ByTechLab/RF---Mostly-3D-Printed-Discone-Antenna/PROJECT_FILES/ECAD/15_DISCONE_V4/1_DISC_PCB_KICAD/_EXPORTED_RENDERS/DISC_PCB_TOP.png

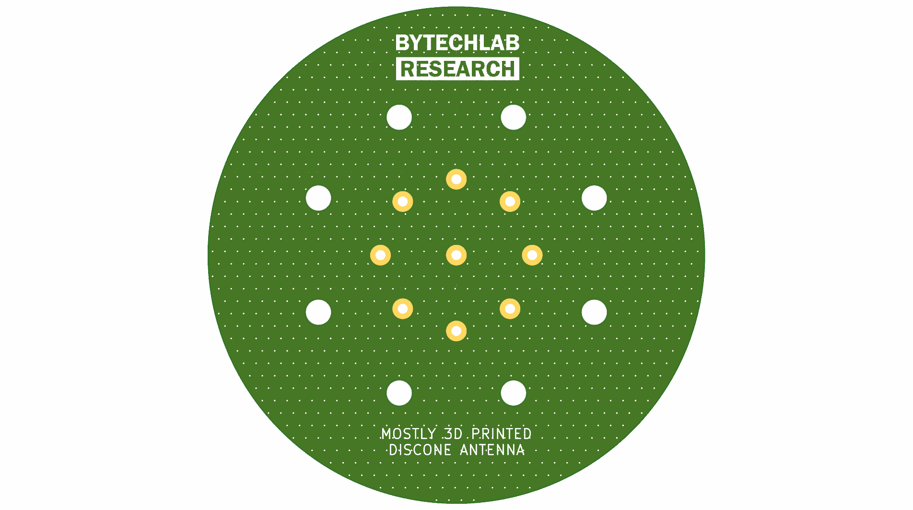
PROJECT_FILES/ECAD/15_DISCONE_V4/1_DISC_PCB_KICAD/_EXPORTED_RENDERS/DISC_PCB_TOP.png
