ByTechLab/RF---Mostly-3D-Printed-Discone-Antenna/PROJECT_FILES/ECAD/15_DISCONE_V4/2_CONE_PCB_KICAD/_EXPORTED_RENDERS/CONE_PCB_TOP.png

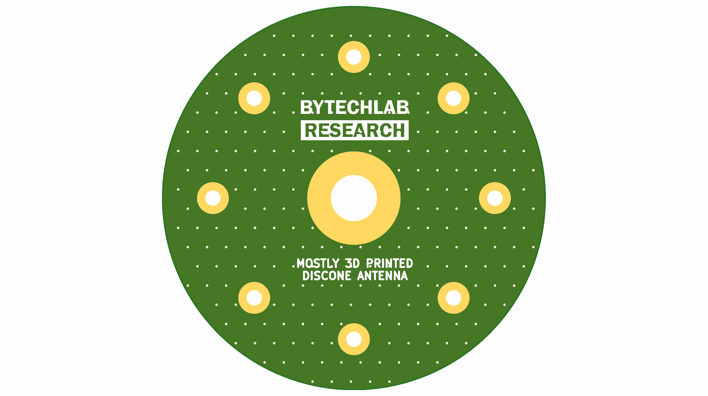
PROJECT_FILES/ECAD/15_DISCONE_V4/2_CONE_PCB_KICAD/_EXPORTED_RENDERS/CONE_PCB_TOP.png
