ByTechLab/RF---Mostly-3D-Printed-Discone-Antenna/PROJECT_FILES/ECAD/15_DISCONE_V4/3_PREAMP_PCB_KICAD/_EXPORTED_RENDERS/PREAMP_PCB_BOTTOM.png

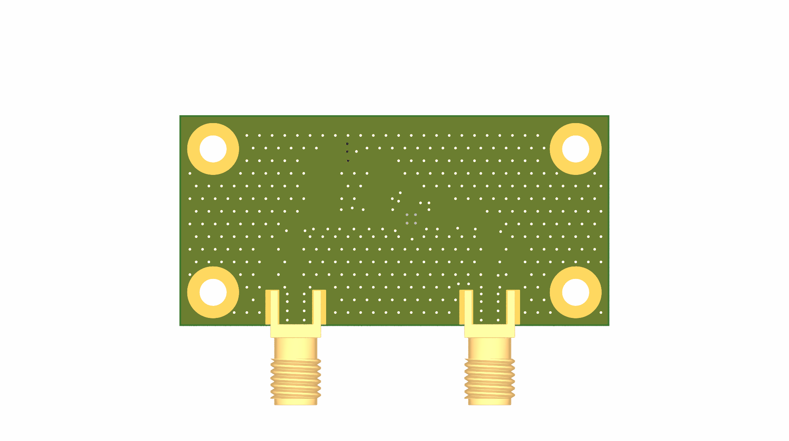
PROJECT_FILES/ECAD/15_DISCONE_V4/3_PREAMP_PCB_KICAD/_EXPORTED_RENDERS/PREAMP_PCB_BOTTOM.png
