ByTechLab/RF---Mostly-3D-Printed-Discone-Antenna/PROJECT_FILES/ECAD/15_DISCONE_V4/4_BIAS_TEE_PCB_KICAD/_EXPORTED_RENDERS/BIAS_TEE_PCB_BOTTOM.png

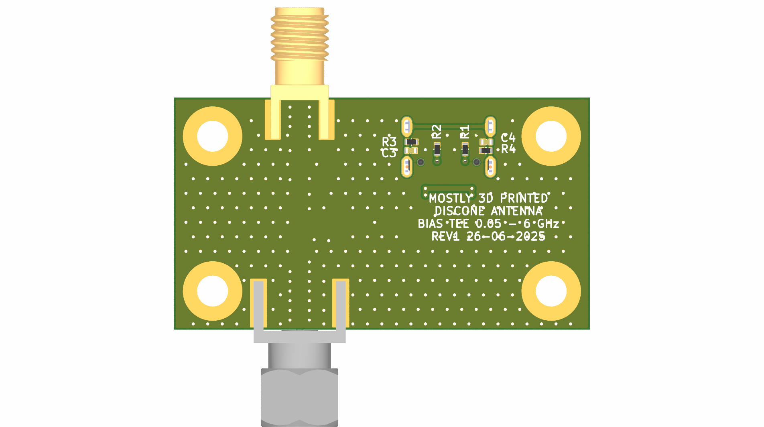
PROJECT_FILES/ECAD/15_DISCONE_V4/4_BIAS_TEE_PCB_KICAD/_EXPORTED_RENDERS/BIAS_TEE_PCB_BOTTOM.png
