ByTechLab/RF---Mostly-3D-Printed-Discone-Antenna/PROJECT_FILES/MCAD/15_DISCONE_V4_KICAD/_STL_EXPORTED/3DP_ASA_Mast_Mount.stl

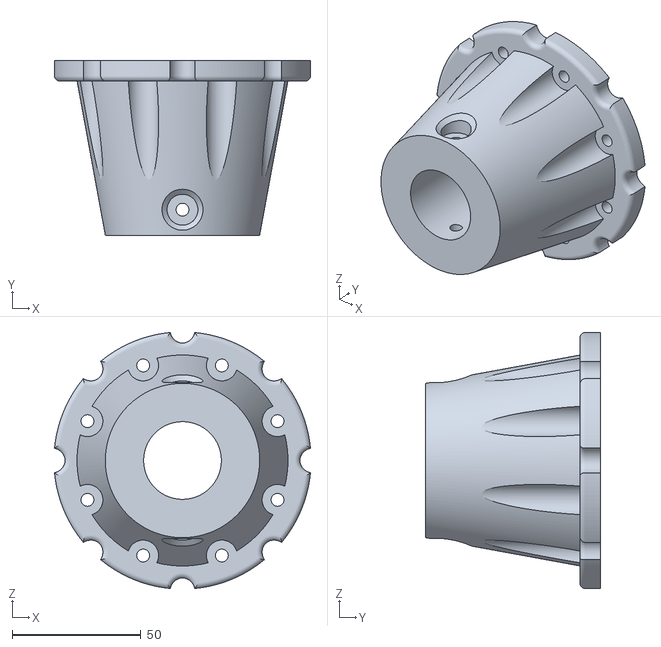
[picture p25: CAD file, 2025-08-10]
PROJECT_FILES/MCAD/15_DISCONE_V4_KICAD/_STL_EXPORTED/3DP_ASA_Mast_Mount.stl
99.5 x 68.0 x 99.5
