ByTechLab/RF---Mostly-3D-Printed-Discone-Antenna/PROJECT_FILES/MCAD/15_DISCONE_V4_KICAD/_STL_EXPORTED/3DP_ASA_Cone_and_Disc_Mount.stl

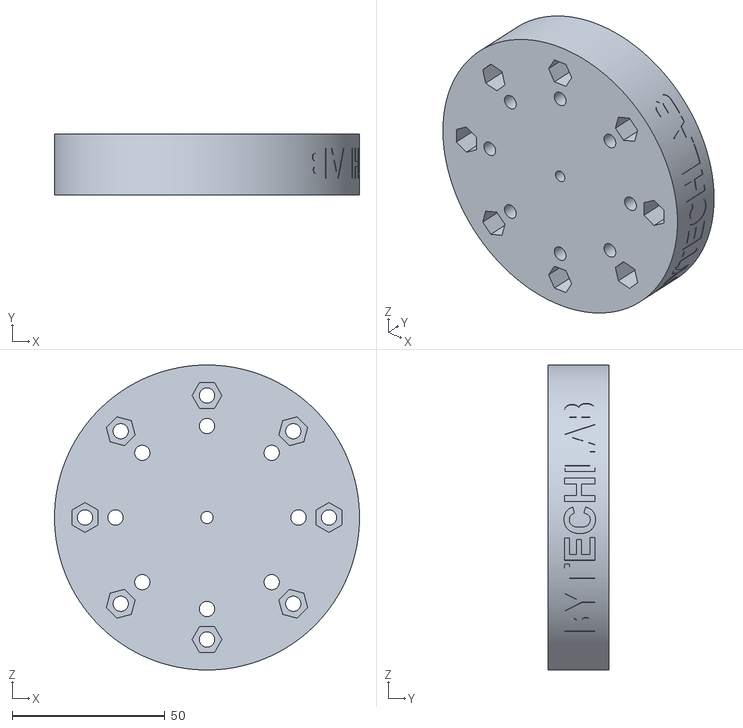
[picture p26: CAD file, 2025-08-10]
PROJECT_FILES/MCAD/15_DISCONE_V4_KICAD/_STL_EXPORTED/3DP_ASA_Cone_and_Disc_Mount.stl
100.0 x 20.0 x 100.0
