ByTechLab/RF---Mostly-3D-Printed-Discone-Antenna/PROJECT_FILES/MCAD/15_DISCONE_V4_KICAD/_STL_EXPORTED/3DP_ASA_Preamp_Case_Bottom.stl

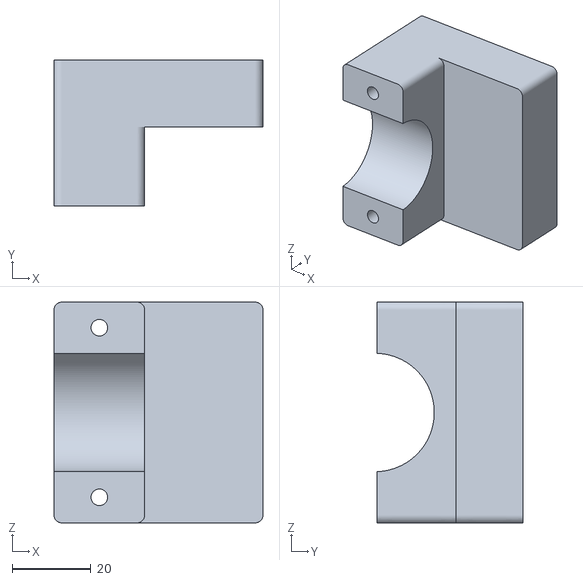
[picture p27: CAD file, 2025-08-10]
PROJECT_FILES/MCAD/15_DISCONE_V4_KICAD/_STL_EXPORTED/3DP_ASA_Preamp_Case_Bottom.stl
53.0 x 37.0 x 56.0
