ByTechLab/RF---Mostly-3D-Printed-Discone-Antenna/PROJECT_FILES/MCAD/15_DISCONE_V4_KICAD/_STL_EXPORTED/3DP_ASA_Preamp_Case_Top.stl

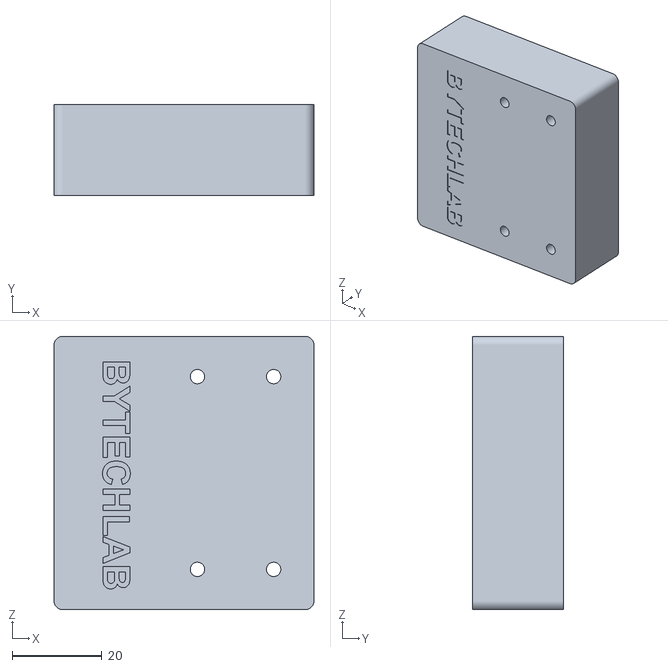
[picture p28: CAD file, 2025-08-10]
PROJECT_FILES/MCAD/15_DISCONE_V4_KICAD/_STL_EXPORTED/3DP_ASA_Preamp_Case_Top.stl
58.0 x 20.2 x 61.0
