ByTechLab/RF---Mostly-3D-Printed-Discone-Antenna/PROJECT_FILES/MCAD/15_DISCONE_V4_KICAD/_STL_EXPORTED/3DP_ASA_Balcony_Mounting_Clamp_Mid.stl

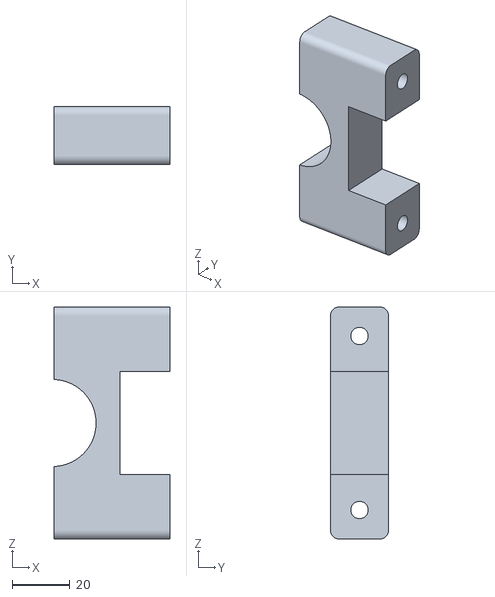
[picture p29: CAD file, 2025-08-10]
PROJECT_FILES/MCAD/15_DISCONE_V4_KICAD/_STL_EXPORTED/3DP_ASA_Balcony_Mounting_Clamp_Mid.stl
40.0 x 20.0 x 80.0
