ByTechLab/RF---Mostly-3D-Printed-Discone-Antenna/PROJECT_FILES/MEASUREMENTS/15_DISCONE_V4/ANT_CABLE_RG58_CU_S21.png

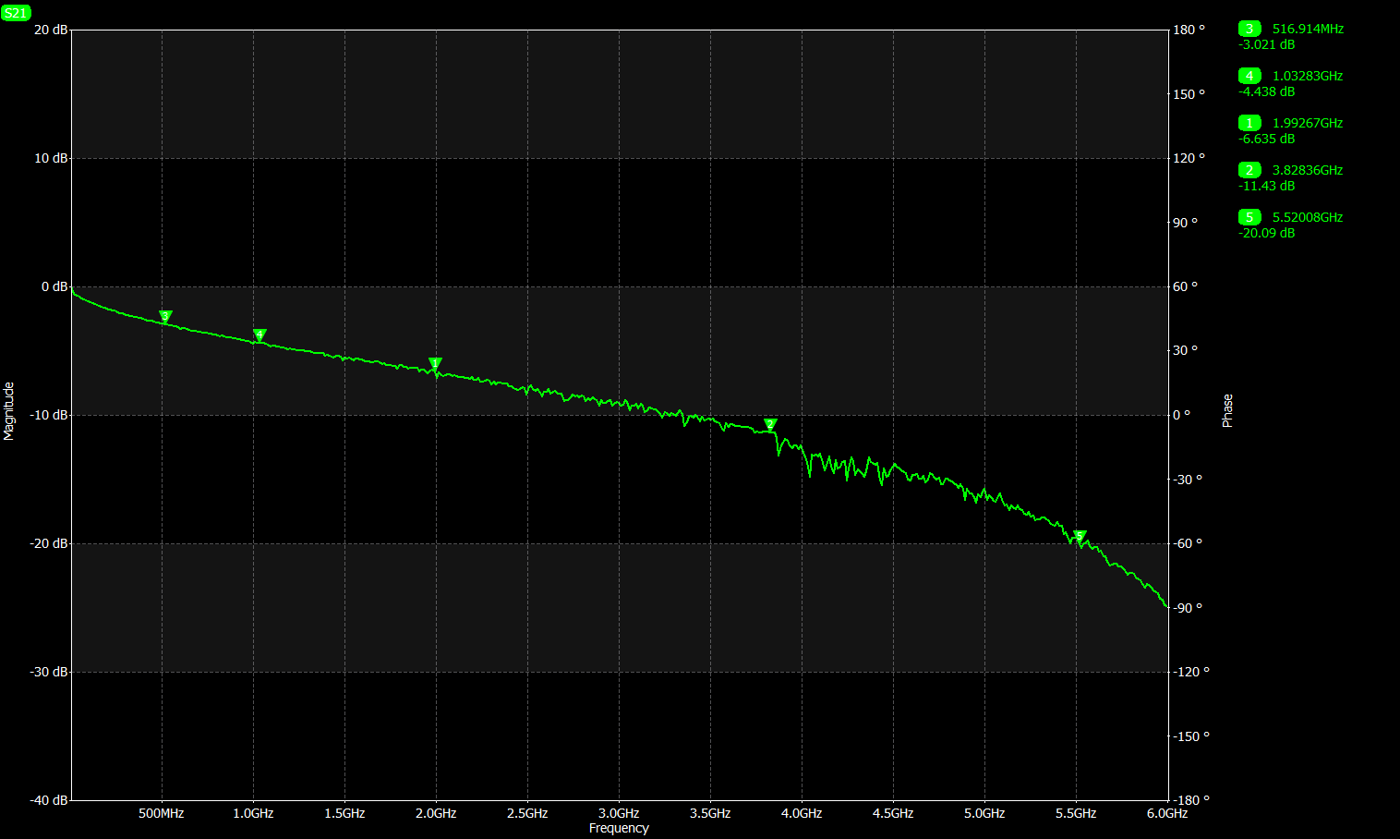
PROJECT_FILES/MEASUREMENTS/15_DISCONE_V4/ANT_CABLE_RG58_CU_S21.png
