ByTechLab/RF---Mostly-3D-Printed-Discone-Antenna/PROJECT_FILES/MEASUREMENTS/15_DISCONE_V4/PREAMP_PCB_MEAS_S11_S22_LOGMAG.png

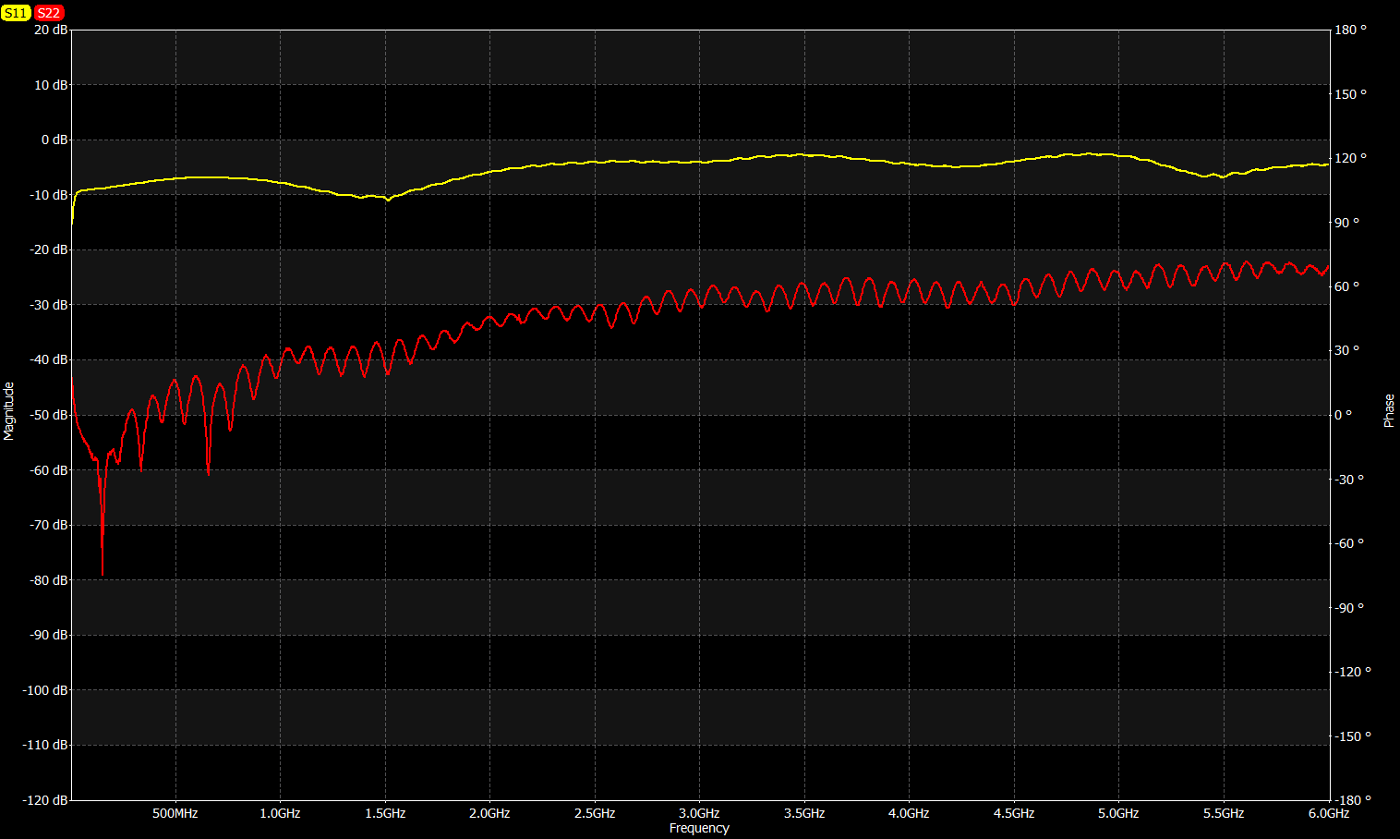
PROJECT_FILES/MEASUREMENTS/15_DISCONE_V4/PREAMP_PCB_MEAS_S11_S22_LOGMAG.png
