ByTechLab/RF---Mostly-3D-Printed-Discone-Antenna/PROJECT_FILES/MEASUREMENTS/15_DISCONE_V4/SDR_2400MHZ.png

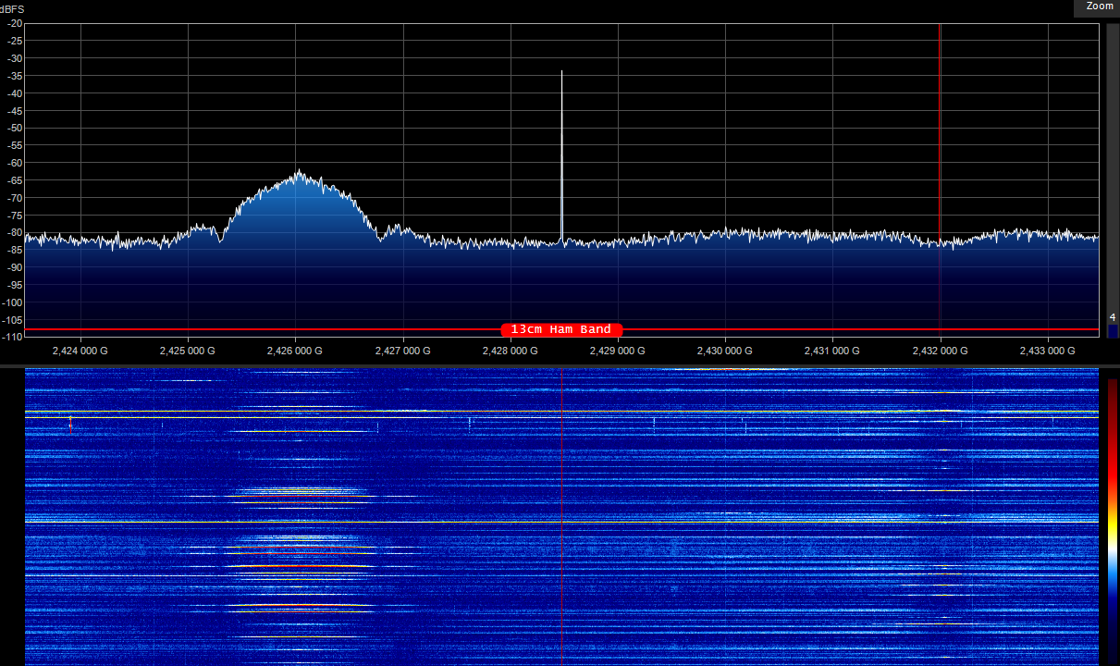
PROJECT_FILES/MEASUREMENTS/15_DISCONE_V4/SDR_2400MHZ.png
