ByTechLab/RF---Mostly-3D-Printed-Discone-Antenna/PROJECT_FILES/ECAD/15_DISCONE_V4/4_BIAS_TEE_PCB_KICAD/_EXPORTED_PDF/PCB/BIAS_TEE_PCB.pdf

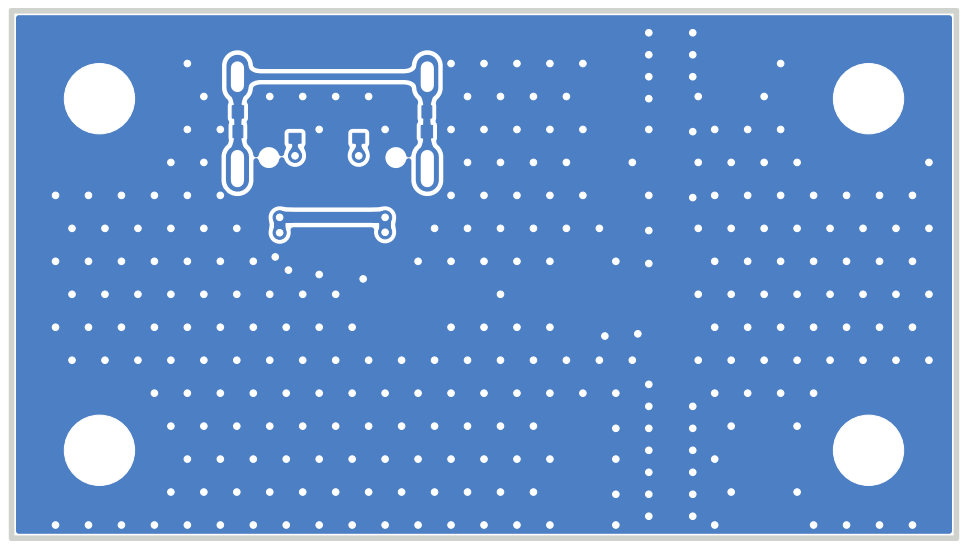
[picture p53: page 1]

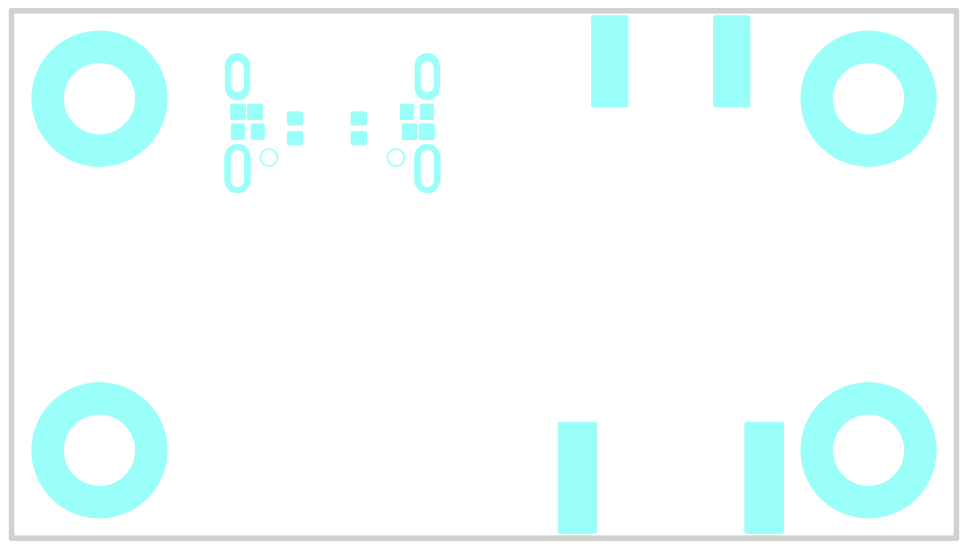
[picture p54: page 2]

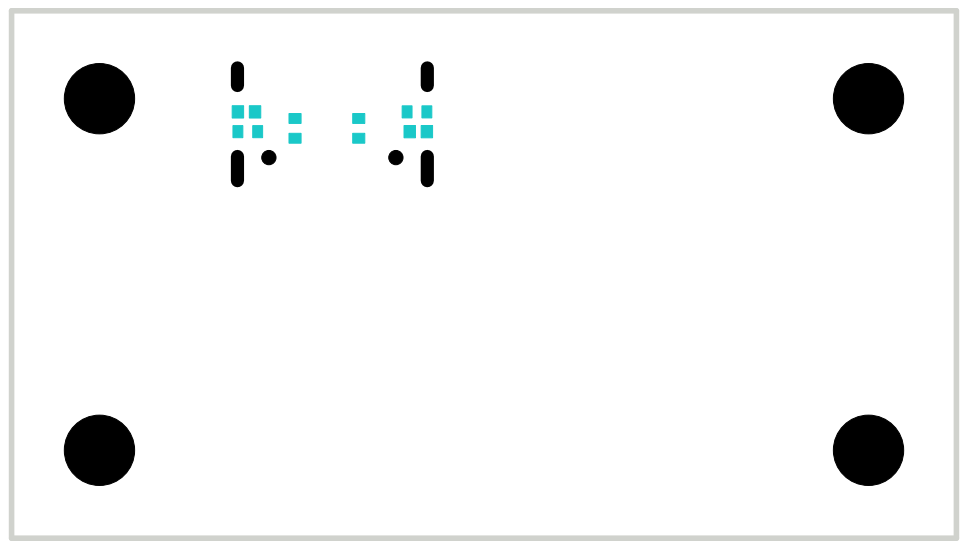
[picture p55: page 3]

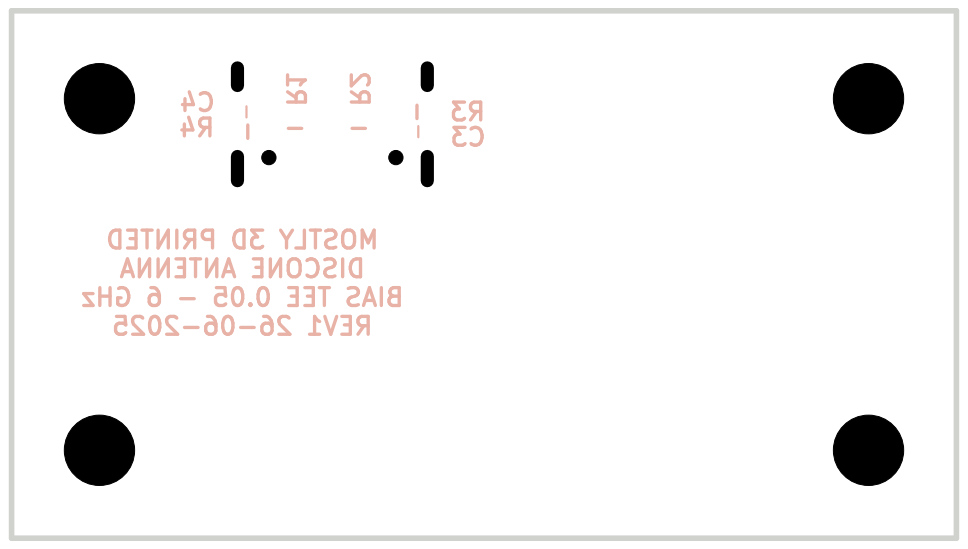
[picture p56: page 4]

ANTENNA DISCONE GHz 6 - 0.05 TEE BIAS

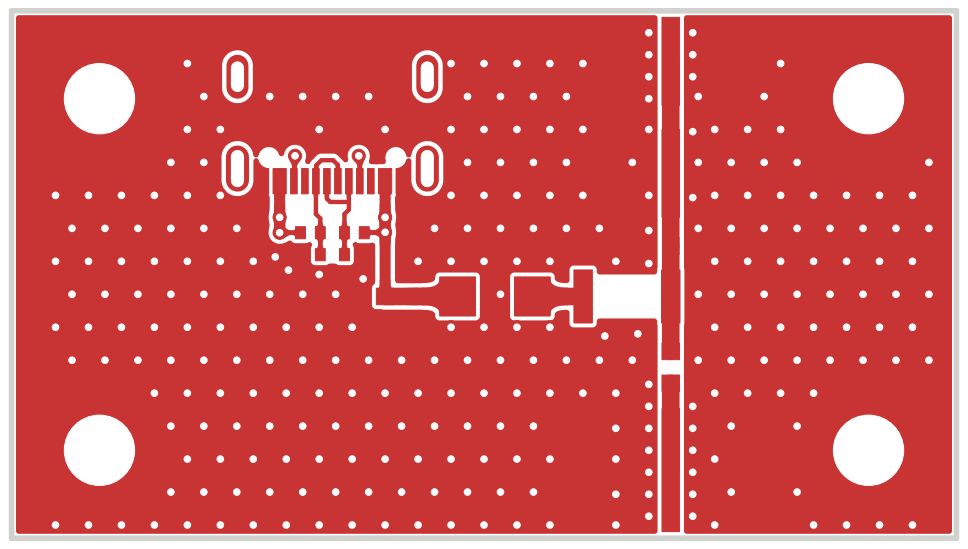
[picture p57: page 5]

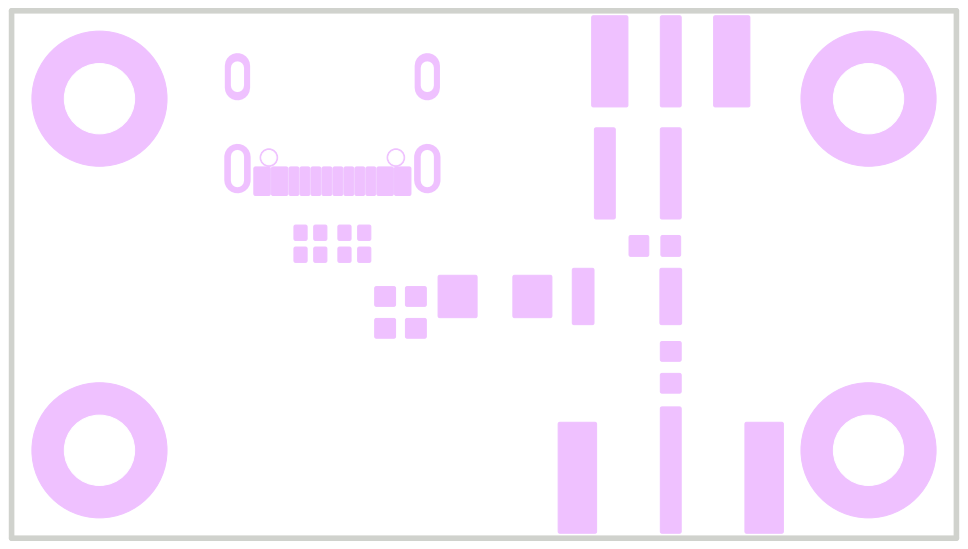
[picture p58: page 6]

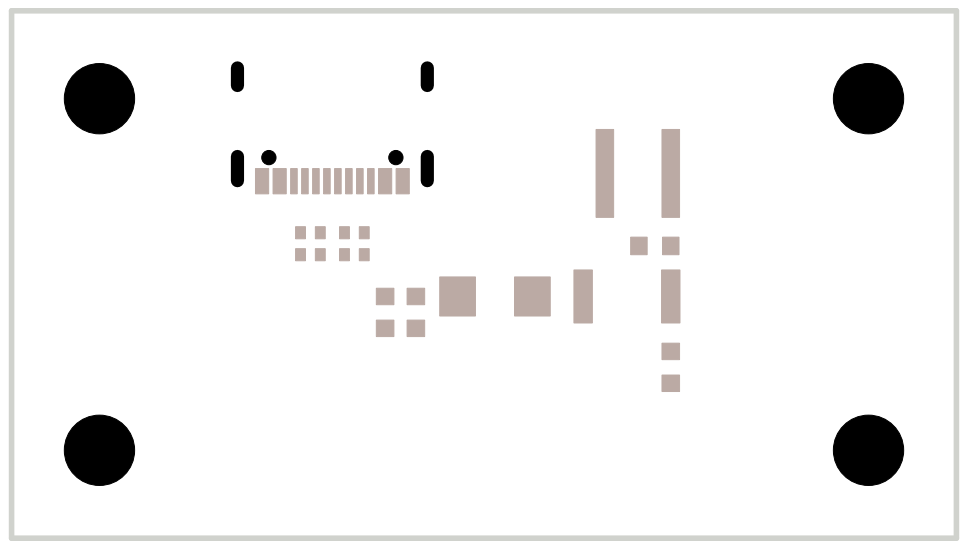
[picture p59: page 7]

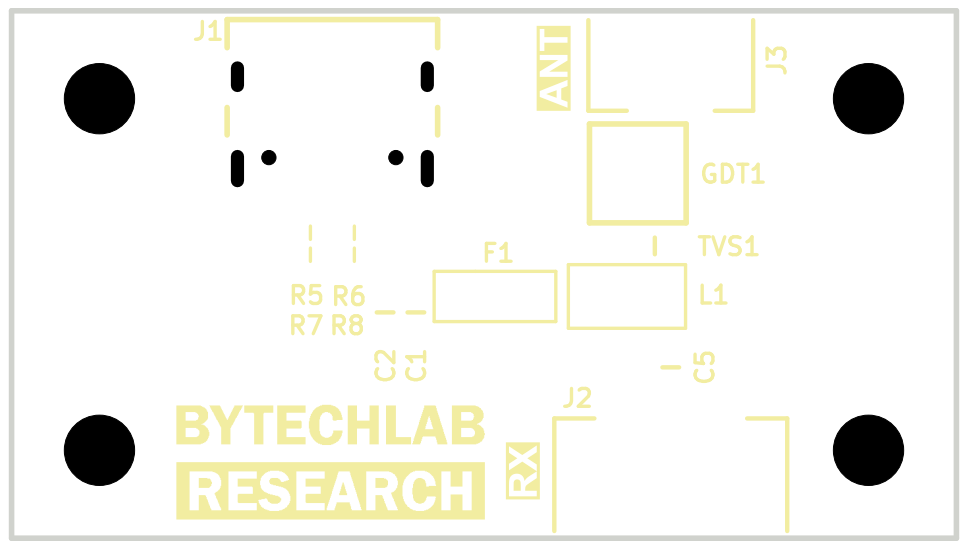
[picture p60: page 8]
