ByTechLab/RF---Mostly-3D-Printed-Discone-Antenna/PROJECT_FILES/ECAD/15_DISCONE_V4/4_BIAS_TEE_PCB_KICAD/_EXPORTED_PDF/SCH/BIAS_TEE_PCB.pdf

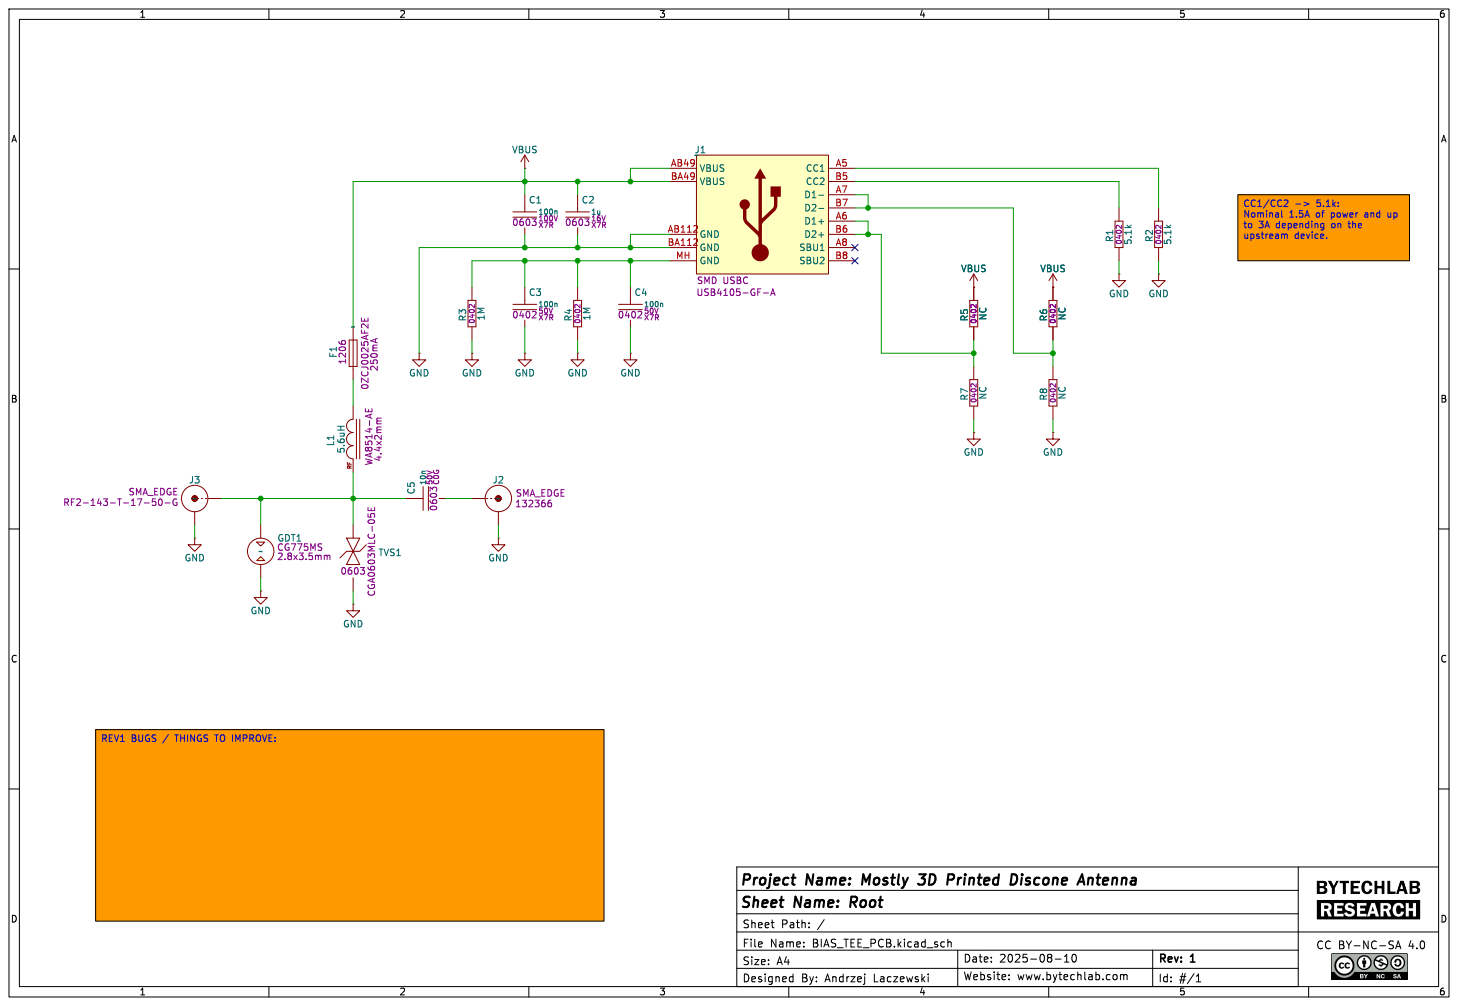
[picture p80: page 1]

REV1 BUGS / THINGS TO IMPROVE:
